tom-f-oconnell/choice/design/reference/Allie/Allie/SURF/Final_presentation/CC2.jpg

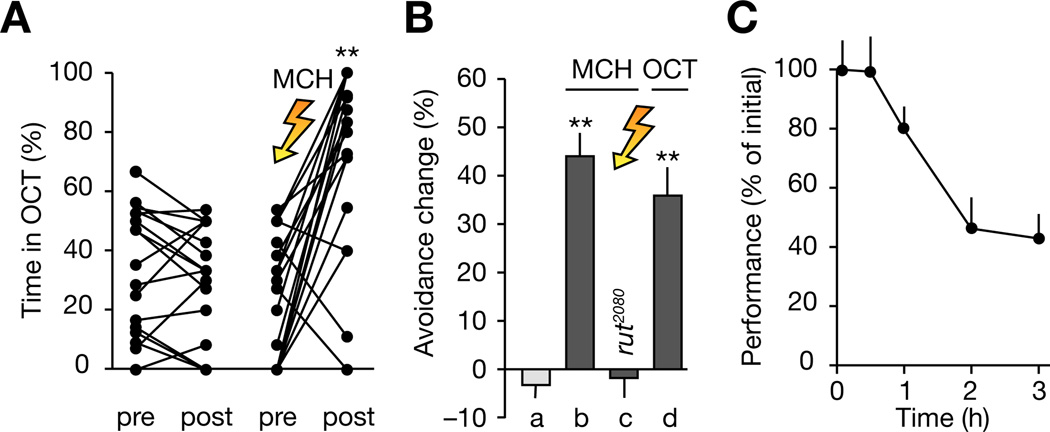
design/reference/Allie/Allie/SURF/Final_presentation/CC2.jpg
