tom-f-oconnell/choice/design/reference/Allie/Allie/SURF/Final_presentation/IMG_1363.JPG

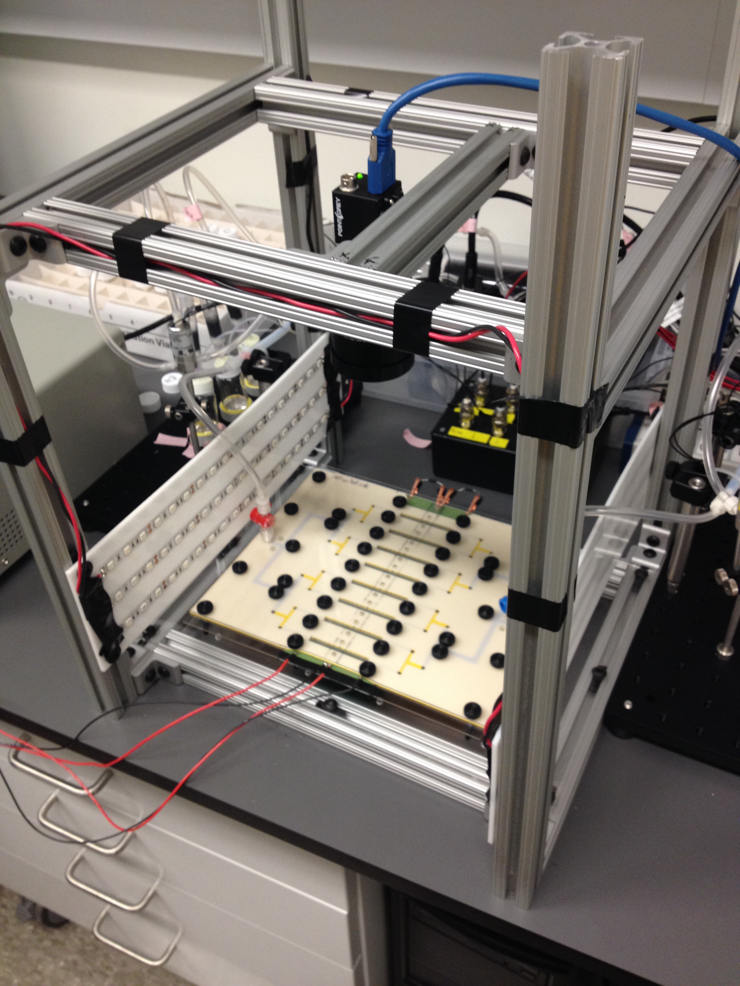
design/reference/Allie/Allie/SURF/Final_presentation/IMG_1363.JPG
