tom-f-oconnell/choice/design/reference/Allie/Allie/SURF/Final_presentation/IMG_1364.JPG

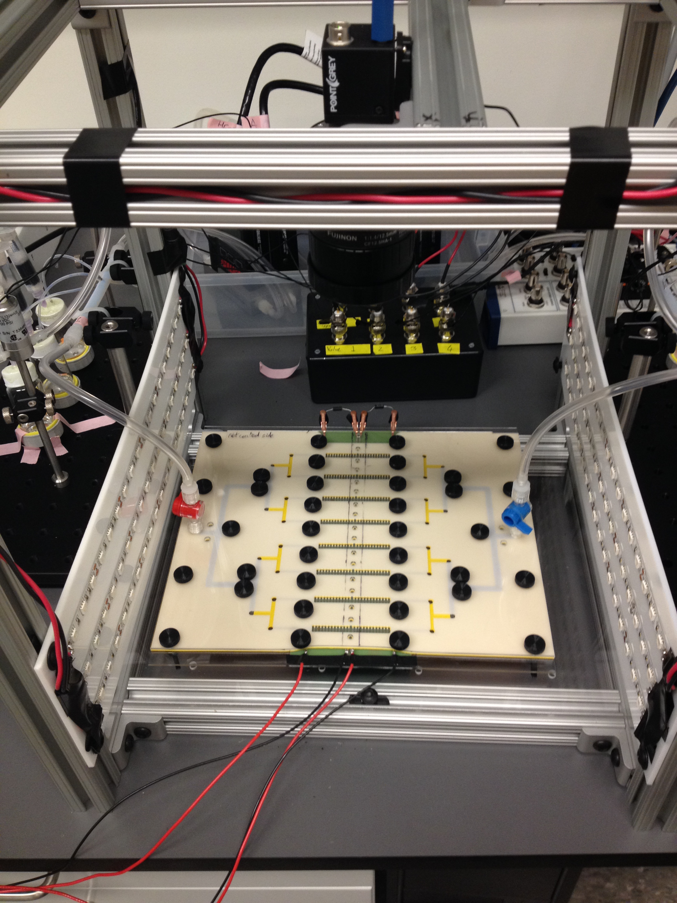
design/reference/Allie/Allie/SURF/Final_presentation/IMG_1364.JPG
