tom-f-oconnell/choice/design/reference/Allie/Allie/SURF/Final_presentation/IMG_1366.JPG

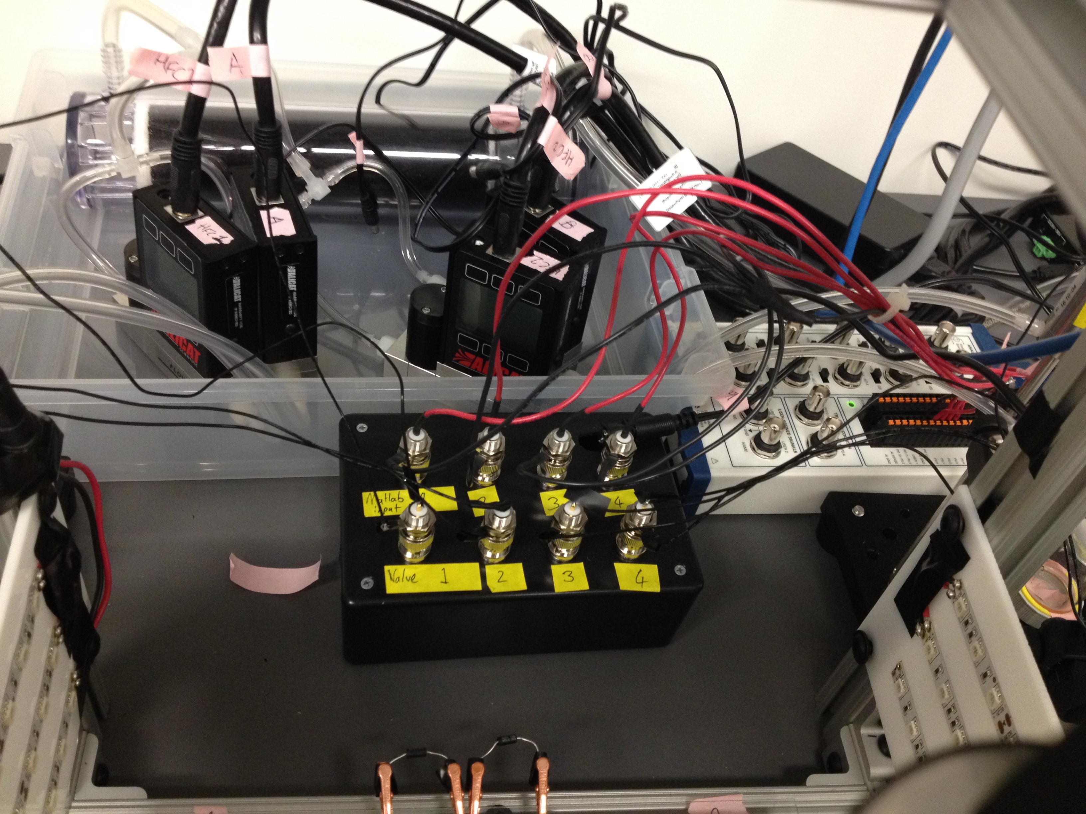
design/reference/Allie/Allie/SURF/Final_presentation/IMG_1366.JPG
