tom-f-oconnell/choice/design/reference/fly_resistance_calculations.jpg

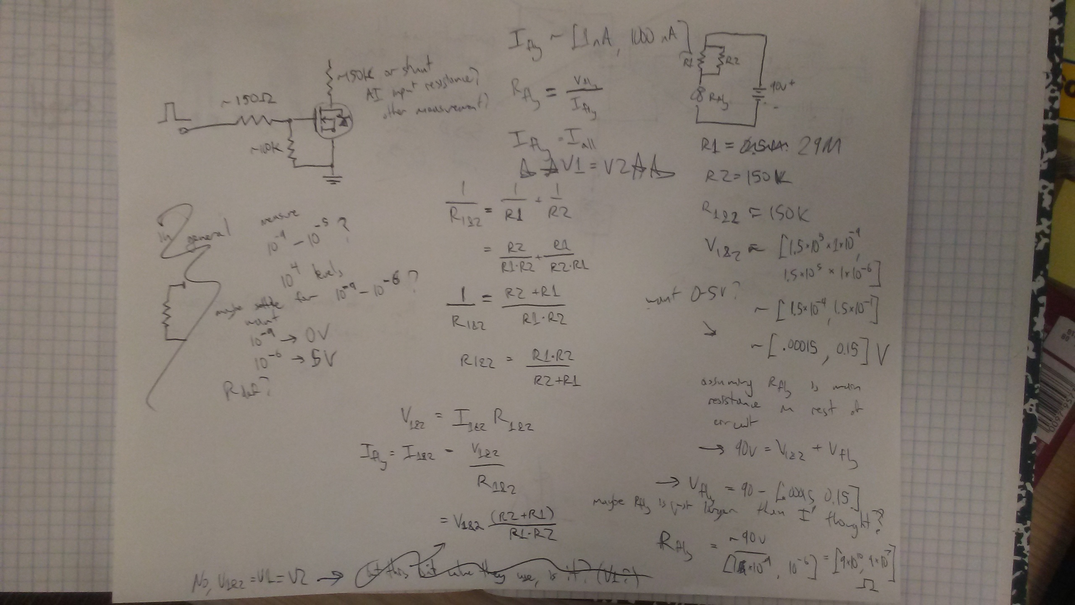
design/reference/fly_resistance_calculations.jpg
