tom-f-oconnell/choice/design/reference/Allie/Behavior_Chamber/Chamber_Design/PCB/Large_board.dxf

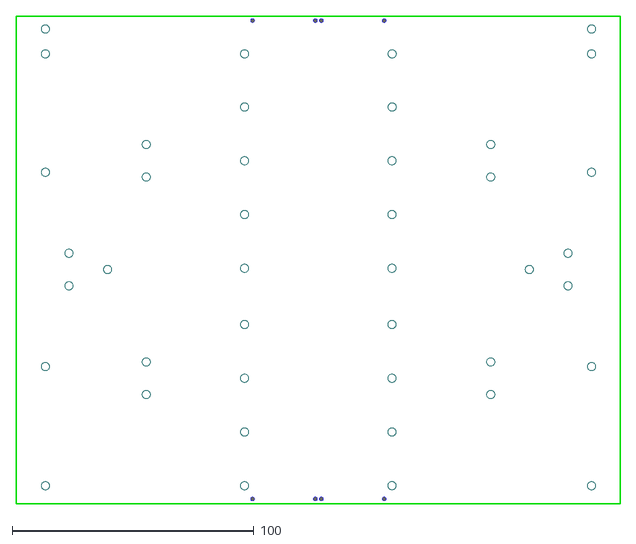
[picture p35: CAD file, 2017-10-18]
design/reference/Allie/Behavior_Chamber/Chamber_Design/PCB/Large_board.dxf
250.0 x 201.8
