tom-f-oconnell/choice/design/reference/Allie/dxfs/PCB_insert.dxf

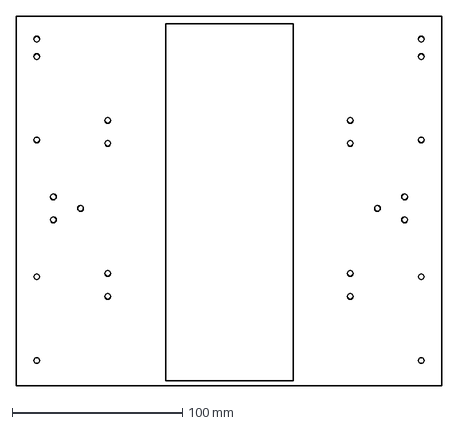
[picture p36: CAD file, 2017-06-18]
design/reference/Allie/dxfs/PCB_insert.dxf
250.0 x 217.4 mm
