tom-f-oconnell/choice/design/reference/Job-022-Flysorter/OuterRing.SLDPRT

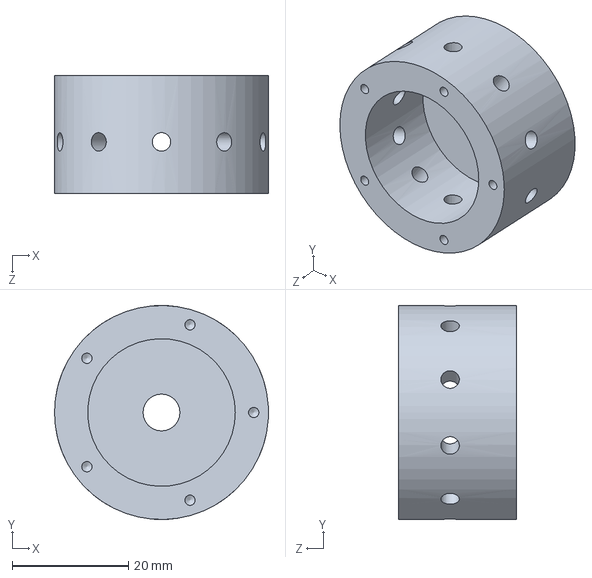
[picture p37: CAD file, 2017-06-15]
design/reference/Job-022-Flysorter/OuterRing.SLDPRT
36.8 x 36.8 x 20.3 mm
