tom-f-oconnell/choice/design/reference/sg90_servo_head.fcstd

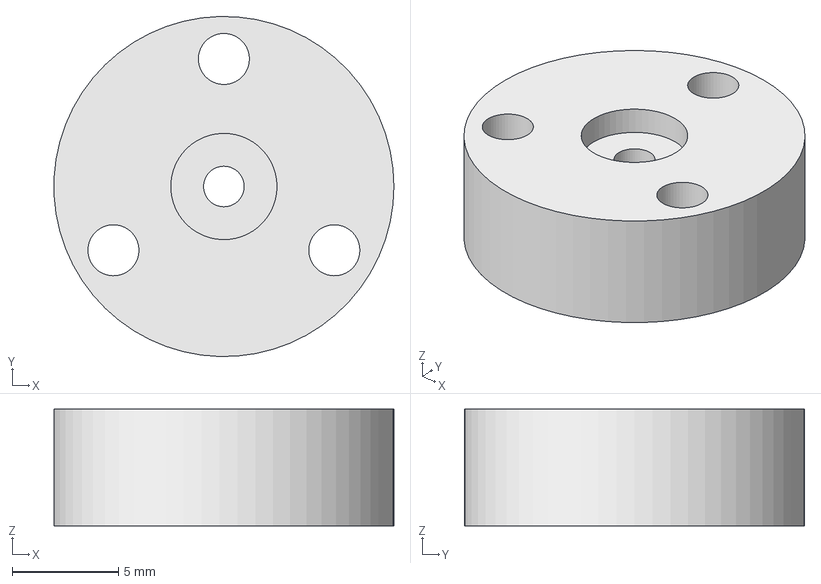
[picture p38: CAD file, 2017-06-14]
design/reference/sg90_servo_head.fcstd
16.0 x 16.0 x 5.50 mm
