tom-f-oconnell/choice/design/lasercut/exploded/pcb_side_gaskets_array.dxf

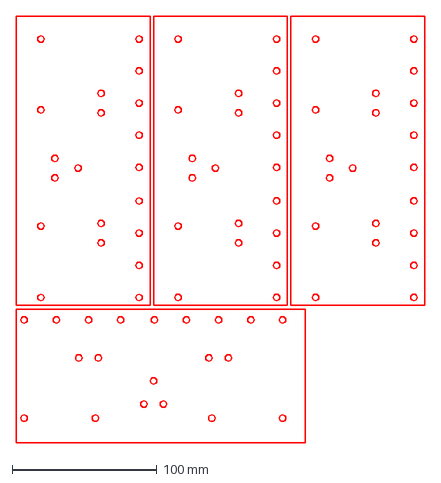
[picture p39: CAD file, 2018-07-19]
design/lasercut/exploded/pcb_side_gaskets_array.dxf
282.5 x 295.0 mm
