tom-f-oconnell/choice/design/print/funnel_servo_arm.stl

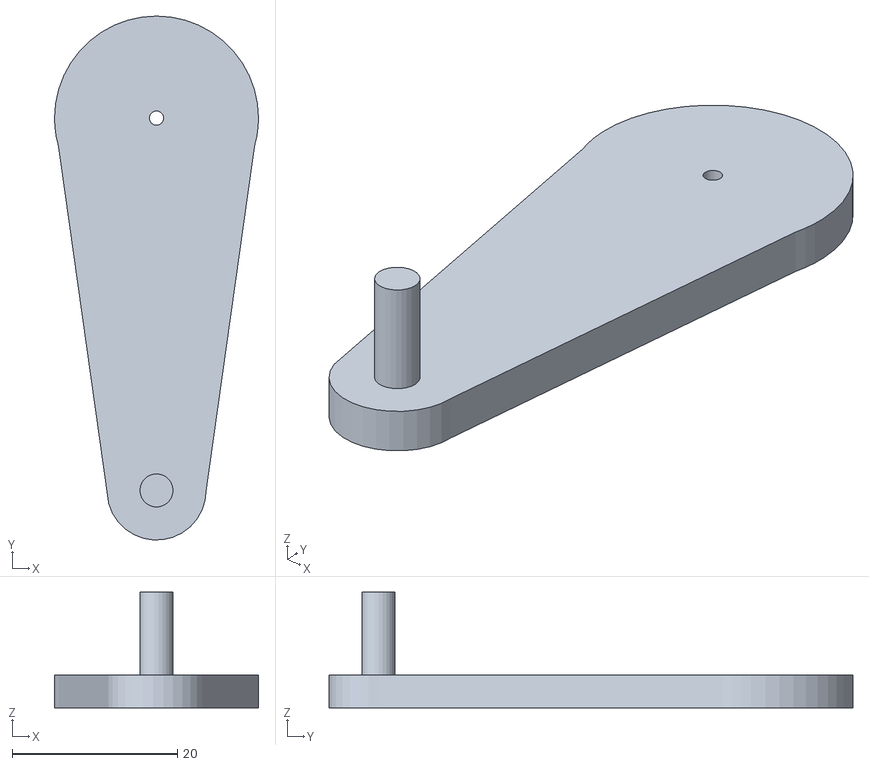
[picture p40: CAD file, 2017-06-14]
design/print/funnel_servo_arm.stl
24.7 x 63.3 x 14.0
