tom-f-oconnell/choice/design/reference/Allie/dxfs/1.dxf

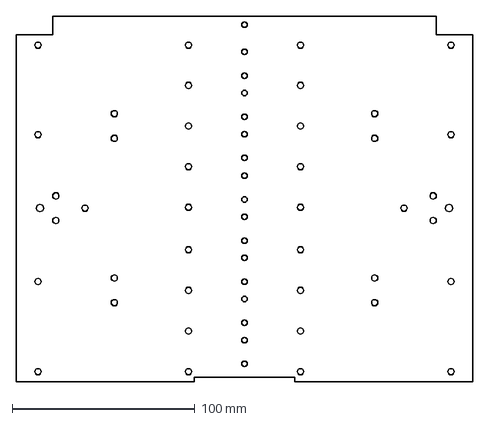
[picture p41: CAD file, 2017-06-18]
design/reference/Allie/dxfs/1.dxf
250.0 x 200.0 mm
