tom-f-oconnell/choice/design/reference/bottom_two_thirds_of_vacuum_trap.fcstd

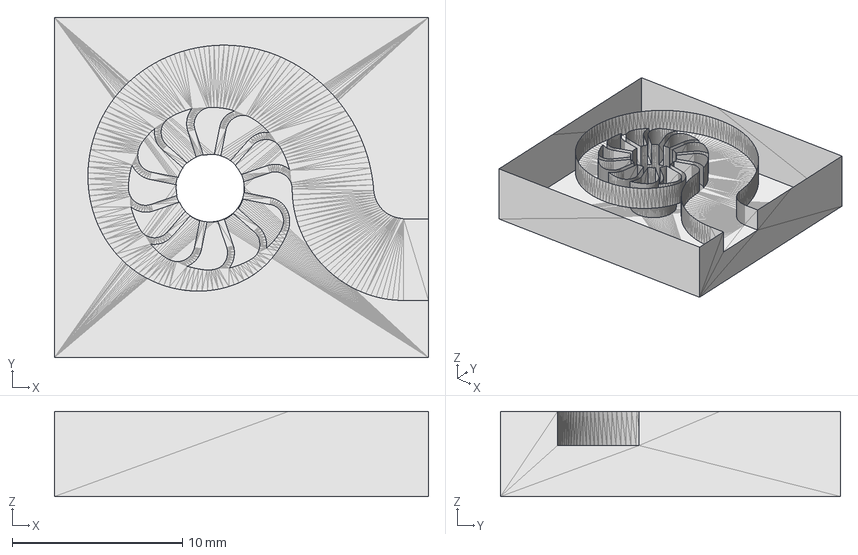
[picture p42: CAD file, 2017-06-14]
design/reference/bottom_two_thirds_of_vacuum_trap.fcstd
22.0 x 20.0 x 5.00 mm
