tom-f-oconnell/choice/design/reference/Job-022-Flysorter/OuterCap.SLDPRT

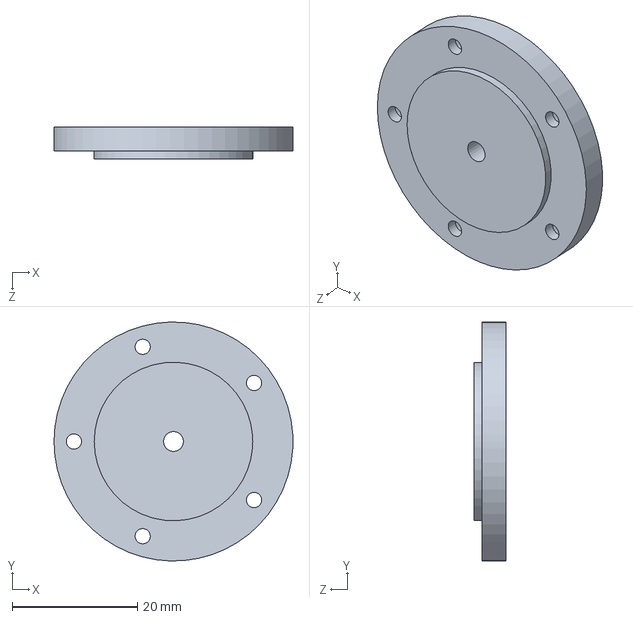
[picture p43: CAD file, 2017-06-15]
design/reference/Job-022-Flysorter/OuterCap.SLDPRT
38.1 x 38.1 x 5.08 mm
