tom-f-oconnell/choice/design/lasercut/mfc_mounting_plate.dxf

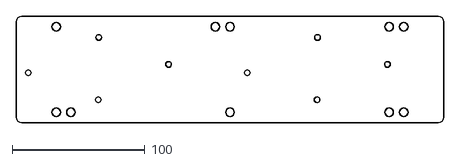
[picture p44: CAD file, 2018-07-19]
design/lasercut/mfc_mounting_plate.dxf
322.0 x 80.0
