tom-f-oconnell/choice/design/print/susan_pulley_around_acrylic.stl

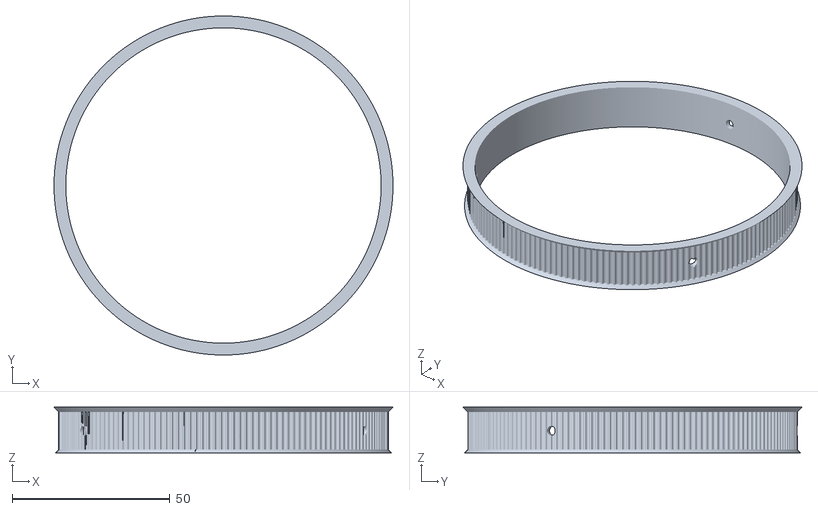
[picture p45: CAD file, 2017-06-14]
design/print/susan_pulley_around_acrylic.stl
107.5 x 107.5 x 14.5
