tom-f-oconnell/choice/design/reference/Allie/dxfs/4.dxf

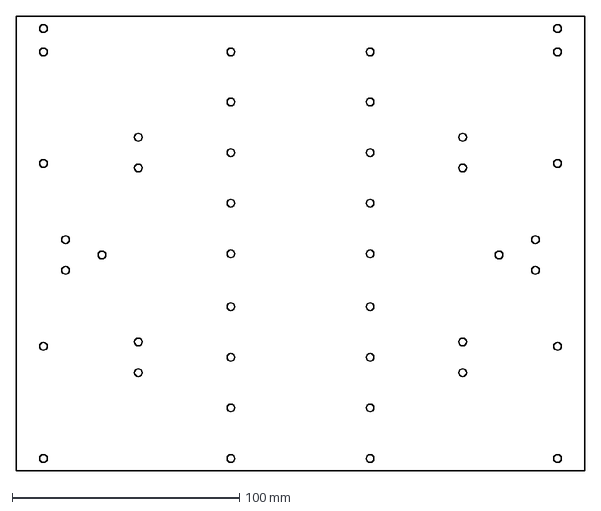
[picture p46: CAD file, 2017-06-18]
design/reference/Allie/dxfs/4.dxf
250.0 x 200.0 mm
