tom-f-oconnell/choice/design/lasercut/box_side.dxf

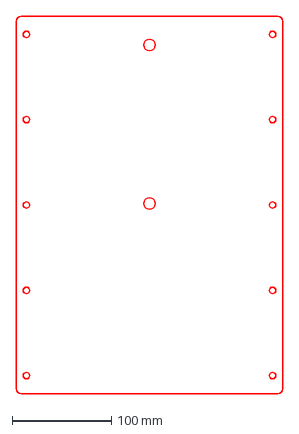
[picture p47: CAD file, 2018-07-19]
design/lasercut/box_side.dxf
268.6 x 381.0 mm
