tom-f-oconnell/choice/design/print/vial_susan_servo_pulley.stl

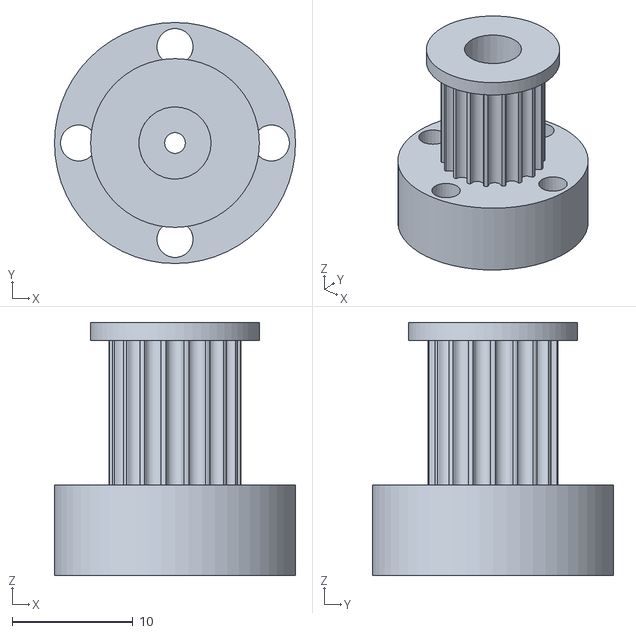
[picture p48: CAD file, 2017-06-14]
design/print/vial_susan_servo_pulley.stl
20.0 x 20.0 x 21.0
