tom-f-oconnell/choice/design/reference/Allie/dxfs/2.dxf

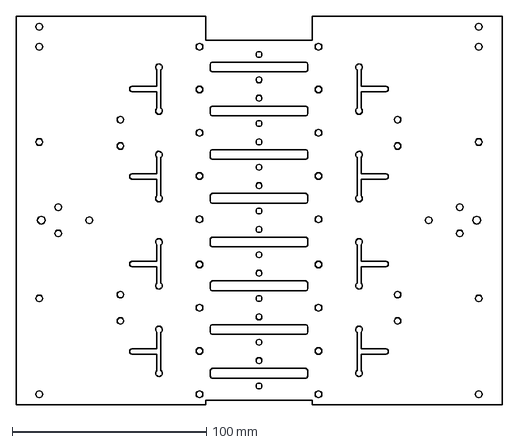
[picture p49: CAD file, 2017-06-18]
design/reference/Allie/dxfs/2.dxf
250.0 x 200.0 mm
