tom-f-oconnell/choice/design/reference/Job-022-Flysorter/InnerCap.SLDPRT

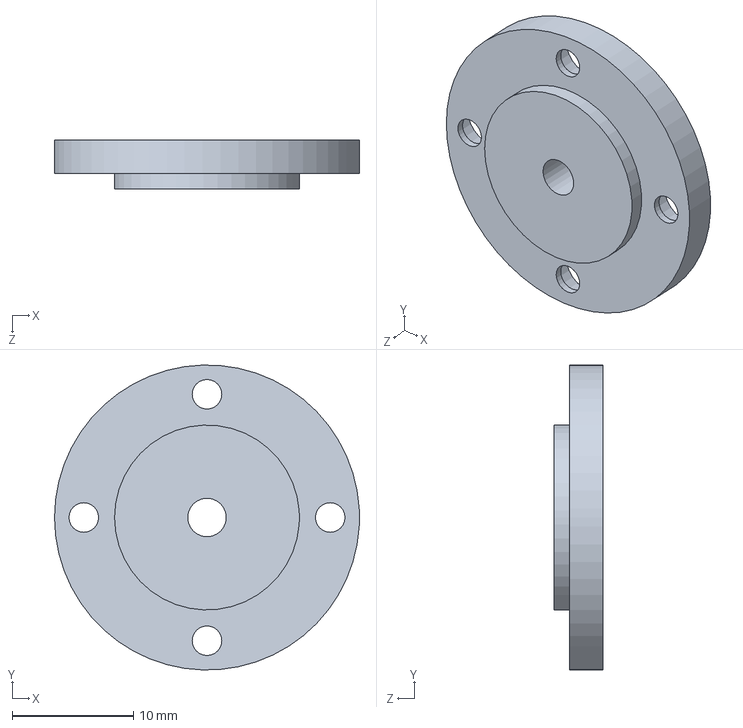
[picture p50: CAD file, 2017-06-15]
design/reference/Job-022-Flysorter/InnerCap.SLDPRT
25.1 x 25.1 x 4.06 mm
