tom-f-oconnell/choice/design/lasercut/floor_pcb_edges.dxf

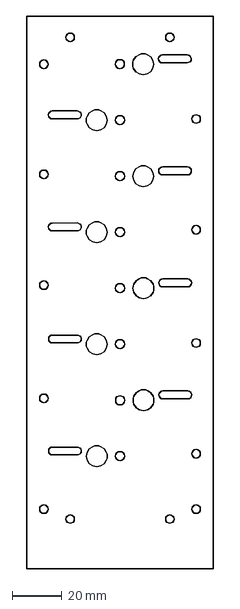
[picture p51: CAD file, 2018-07-19]
design/lasercut/floor_pcb_edges.dxf
75.0 x 222.0 mm
