tom-f-oconnell/choice/design/print/susan_bearing_support.stl

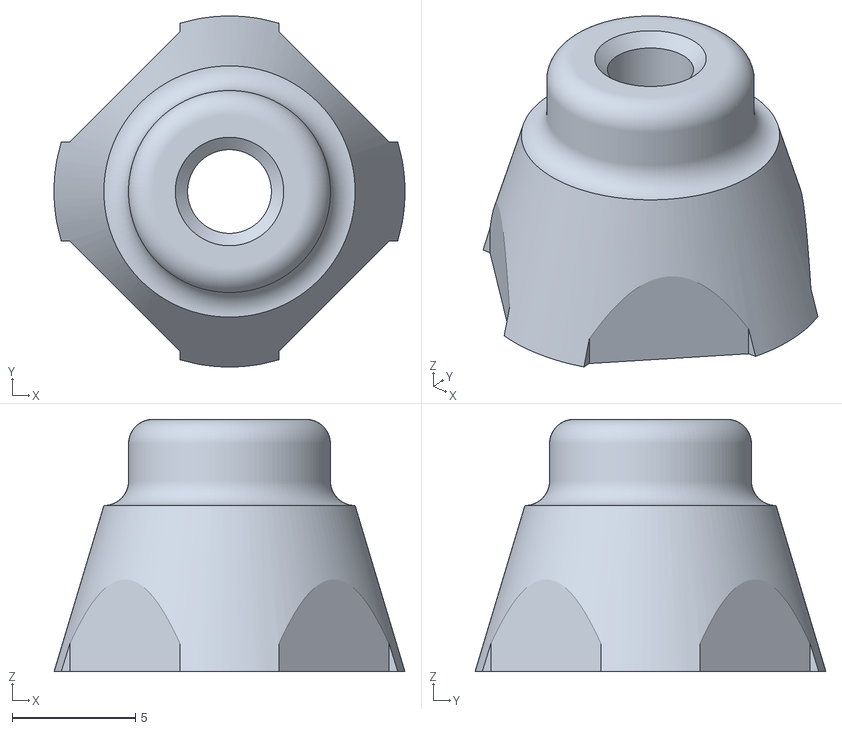
[picture p52: CAD file, 2017-06-14]
design/print/susan_bearing_support.stl
14.2 x 14.2 x 10.2
