tom-f-oconnell/choice/design/lasercut/humidifier_bottle_brace.dxf

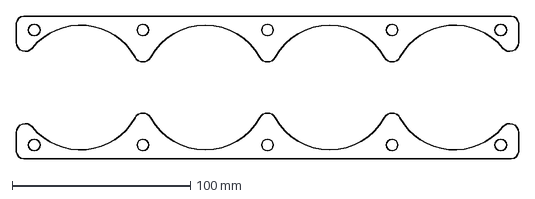
[picture p54: CAD file, 2018-07-19]
design/lasercut/humidifier_bottle_brace.dxf
282.0 x 80.0 mm
