tom-f-oconnell/choice/design/reference/Allie/dxfs/LED_side.dxf

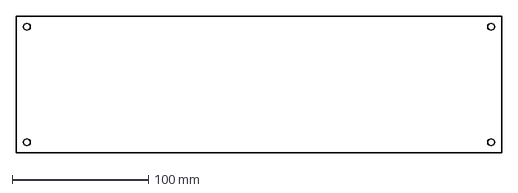
[picture p55: CAD file, 2017-06-17]
design/reference/Allie/dxfs/LED_side.dxf
355.6 x 100.0 mm
