tom-f-oconnell/choice/design/lasercut/inside_plate_with_slots.dxf

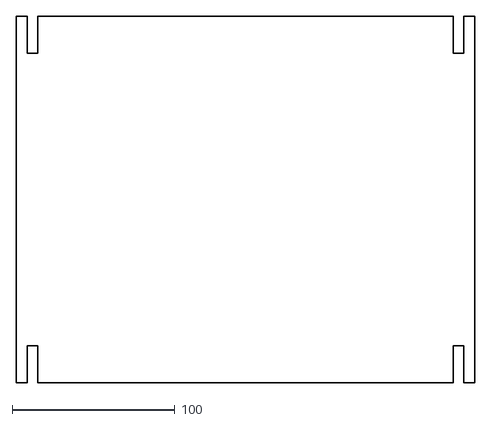
[picture p56: CAD file, 2018-07-19]
design/lasercut/inside_plate_with_slots.dxf
282.0 x 225.6
