tom-f-oconnell/choice/design/reference/Allie/dxfs/LED.dxf

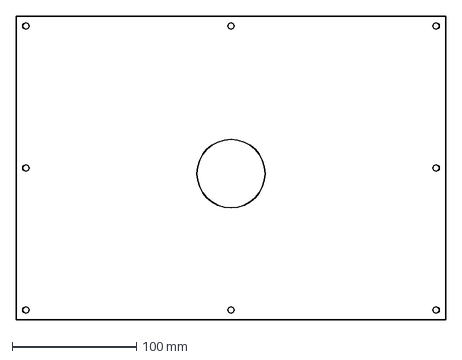
[picture p57: CAD file, 2017-06-17]
design/reference/Allie/dxfs/LED.dxf
345.6 x 244.0 mm
