tom-f-oconnell/choice/design/lasercut/humidifier_bottle_mount_bottom.dxf

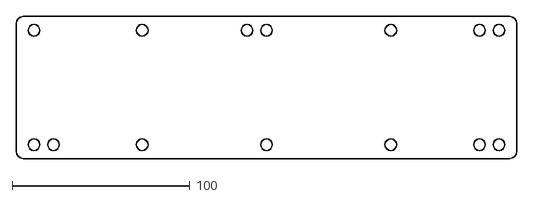
[picture p58: CAD file, 2018-07-19]
design/lasercut/humidifier_bottle_mount_bottom.dxf
282.0 x 80.0
