tom-f-oconnell/choice/design/reference/Allie/dxfs/Frame.dxf

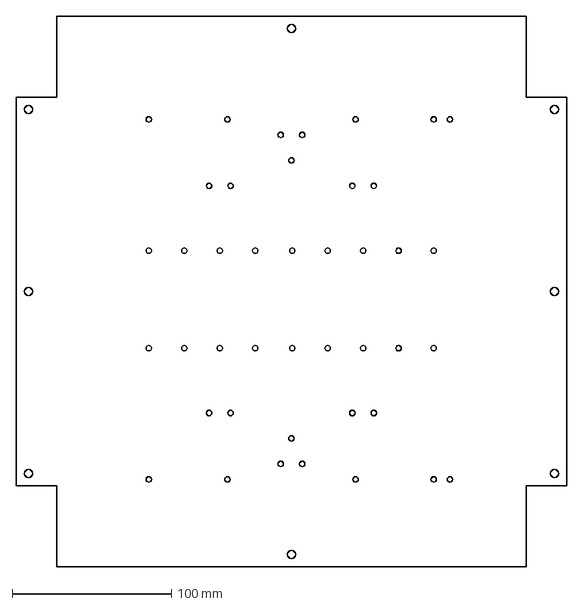
[picture p59: CAD file, 2017-06-17]
design/reference/Allie/dxfs/Frame.dxf
345.6 x 345.6 mm
