tom-f-oconnell/choice/design/lasercut/ceiling_pcb_edges.dxf

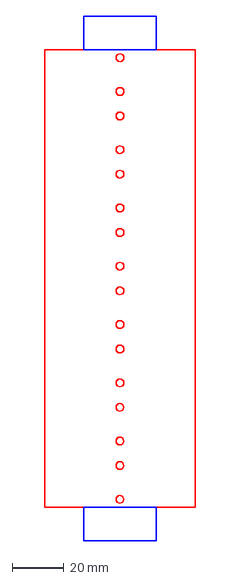
[picture p60: CAD file, 2018-02-15]
design/lasercut/ceiling_pcb_edges.dxf
58.0 x 202.5 mm
