tom-f-oconnell/choice/design/lasercut/modular_vacuum_trap.dxf

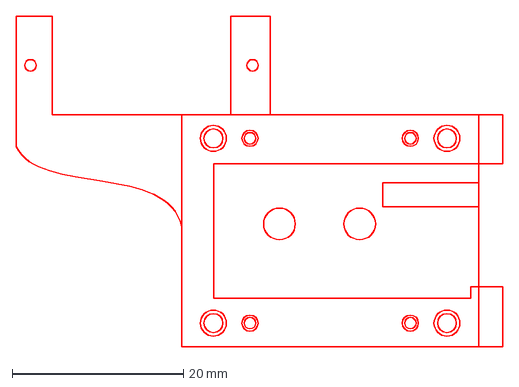
[picture p61: CAD file, 2017-06-28]
design/lasercut/modular_vacuum_trap.dxf
56.9 x 38.7 mm
