tom-f-oconnell/choice/design/lasercut/shaft_output_doubler.dxf

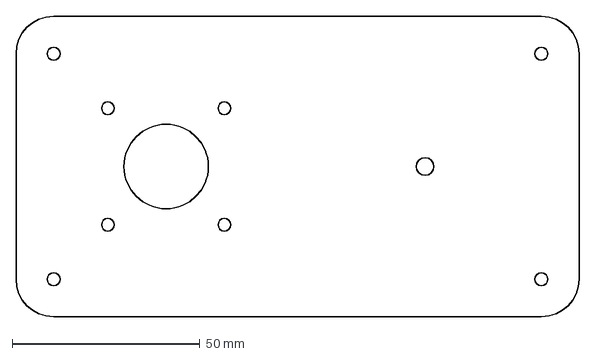
[picture p62: CAD file, 2017-06-22]
design/lasercut/shaft_output_doubler.dxf
150.0 x 80.0 mm
