tom-f-oconnell/choice/design/lasercut/smaller_boardcam_mount.dxf

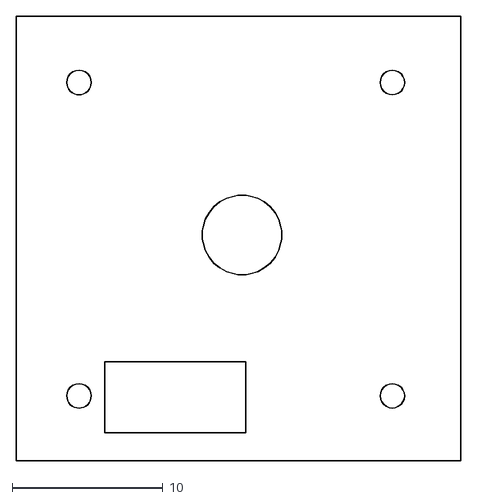
[picture p63: CAD file, 2017-06-16]
design/lasercut/smaller_boardcam_mount.dxf
29.5 x 29.5
