tom-f-oconnell/choice/design/lasercut/vacuum_trap_for_engraving_0.3.dxf

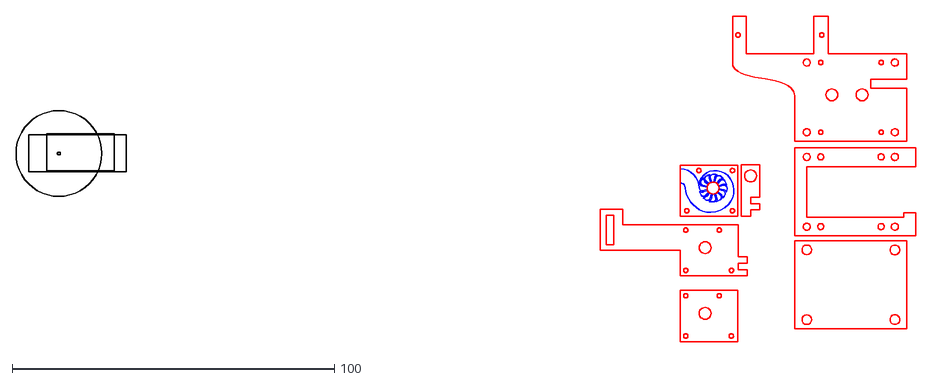
[picture p64: CAD file, 2017-06-16]
design/lasercut/vacuum_trap_for_engraving_0.3.dxf
279.2 x 100.9
