tom-f-oconnell/choice/design/lasercut/make_3d/2.1_delrin_chambers_and_manifold.scad

color(c = [1, 1, 1, 0.9000000000]) {
	translate(v = [0, 0, 17.8594000000]) {
		dxf_linear_extrude(file = "../olfactory_shock_conditioning_chambers.dxf", height = 0.7938000000, layer = "2.1_delrin_chambers_and_manifold");
	}
}
