tom-f-oconnell/choice/design/lasercut/make_3d/3.1_yellow_manifold_layer.scad

color(c = [1, 1, 0, 0.9500000000]) {
	translate(v = [0, 0, 17.4625000000]) {
		dxf_linear_extrude(file = "../olfactory_shock_conditioning_chambers.dxf", height = 0.3969000000, layer = "3.1_yellow_manifold_layer");
	}
}
