tom-f-oconnell/choice/design/lasercut/make_3d/4.1_pcb_side_spacers.scad

color(c = [0, 0, 0, 1]) {
	translate(v = [0, 0, 15.8750000000]) {
		dxf_linear_extrude(file = "../olfactory_shock_conditioning_chambers.dxf", height = 1.5875000000, layer = "4.1_pcb_side_spacers");
	}
}
