tom-f-oconnell/choice/design/lasercut/make_3d/6.1_vacuum_trap_guides.scad

color(c = [1, 1, 1, 0.2000000000]) {
	translate(v = [0, 0, 9.5250000000]) {
		dxf_linear_extrude(file = "../olfactory_shock_conditioning_chambers.dxf", height = 3.1750000000, layer = "6.1_vacuum_trap_guides");
	}
}
