tom-f-oconnell/choice/design/lasercut/make_3d/7_vacuum_trap_sliders.scad

color(c = [1, 1, 1, 0.2000000000]) {
	translate(v = [0, 0, 6.3500000000]) {
		dxf_linear_extrude(file = "../olfactory_shock_conditioning_chambers.dxf", height = 3.1750000000, layer = "7_vacuum_trap_sliders");
	}
}
