tom-f-oconnell/choice/design/lasercut/make_3d/8_flow_regulator_retainers.scad

color(c = [1, 1, 1, 0.2000000000]) {
	translate(v = [0, 0, 3.1750000000]) {
		dxf_linear_extrude(file = "../olfactory_shock_conditioning_chambers.dxf", height = 3.1750000000, layer = "8_flow_regulator_retainers");
	}
}
